lspr98/bike-computer-32/software/esp32/esp32c3-bike-companion-32/include/screens.h

#ifndef _SCREENS_H
#define _SCREENS_H

#include <Arduino.h>
#include <screenelements.h>
#include <vector>
#include <sharedspidisplay.h>
#include <globalconfig.h>

/*

    Definition of UI-screens

*/


/*

    Parent class for UI-screens

*/
class Screen {

protected:
    uint64_t _tick;
    std::vector<ScreenElement*> _elements;

public:
    Screen() : hasStatusBar(false), hasMap(false) {};
    bool hasStatusBar, hasMap;
    virtual void reset() = 0;
    virtual bool render(SharedSPIDisplay* display) = 0;
};


class BootScreen : public Screen {

private:
    int textSize = 2;
    int spinnerSize = 15;
    int rows[5] = {5, 35, 65, 95, 125};
    int cols[2] = {5, 120};

    ScreenText _labelDisplay = ScreenText(cols[0], rows[0], textSize, "Display");
    ScreenText _labelGnss = ScreenText(cols[0], rows[1], textSize, "GNSS");
    ScreenText _labelSD = ScreenText(cols[0], rows[2], textSize, "SDCard");
    ScreenText _labelMap = ScreenText(cols[0], rows[3], textSize, "Map");
    ScreenText _labelTrack = ScreenText(cols[0], rows[4], textSize, "Track");

    // Note: these labels are used as center elements for the spinners. Do not add them to the _elements list.
    ScreenText _checkDisplay = ScreenText(cols[1], rows[0], textSize, "OK");
    ScreenText _checkGnss = ScreenText(cols[1], rows[1], textSize, "OK");
    ScreenText _checkSD = ScreenText(cols[1], rows[2], textSize, "OK");
    ScreenText _checkMap = ScreenText(cols[1], rows[3], textSize, "OK");
    ScreenText _checkTrack = ScreenText(cols[1], rows[4], textSize, "OK");

    ScreenDoubleCircleSpinner _spinnerDisplay = ScreenDoubleCircleSpinner(cols[1], rows[0], spinnerSize, &_checkDisplay);
    ScreenDoubleCircleSpinner _spinnerGnss = ScreenDoubleCircleSpinner(cols[1], rows[1], spinnerSize, &_checkGnss);
    ScreenDoubleCircleSpinner _spinnerSD = ScreenDoubleCircleSpinner(cols[1], rows[2], spinnerSize, &_checkSD);
    ScreenDoubleCircleSpinner _spinnerMap = ScreenDoubleCircleSpinner(cols[1], rows[3], spinnerSize, &_checkMap);
    ScreenDoubleCircleSpinner _spinnerTrack = ScreenDoubleCircleSpinner(cols[1], rows[4], spinnerSize, &_checkTrack);

public:
    int8_t displayOK, gnssOK, mapOK, sdOK, trackOK;

    BootScreen() : Screen(), displayOK(0), gnssOK(0), mapOK(0), sdOK(0), trackOK(0) {

        _elements.push_back(&_labelDisplay);
        _elements.push_back(&_labelGnss);
        _elements.push_back(&_labelMap);
        _elements.push_back(&_labelSD);
        _elements.push_back(&_labelTrack);
        _elements.push_back(&_spinnerDisplay);
        _elements.push_back(&_spinnerGnss);
        _elements.push_back(&_spinnerMap);
        _elements.push_back(&_spinnerSD);
        _elements.push_back(&_spinnerTrack);
    };

    void reset() {

    };

    bool render(SharedSPIDisplay* display) {
        // Update elements based on status
        if(displayOK < 0) _checkDisplay.setText("ER");
        if(gnssOK < 0) _checkGnss.setText("ER");
        if(sdOK < 0) _checkSD.setText("ER");
        if(mapOK < 0) _checkMap.setText("ER");
        if(trackOK < 0) _checkTrack.setText("ER");

        _spinnerDisplay.setStatic(displayOK != 0);
        _spinnerDisplay.setCenterVisiblilty(displayOK != 0);
        _spinnerGnss.setStatic(gnssOK != 0);
        _spinnerGnss.setCenterVisiblilty(gnssOK != 0);
        _spinnerSD.setStatic(sdOK != 0);
        _spinnerSD.setCenterVisiblilty(sdOK != 0);
        _spinnerMap.setStatic(mapOK != 0);
        _spinnerMap.setCenterVisiblilty(mapOK != 0);
        _spinnerTrack.setStatic(trackOK != 0);
        _spinnerTrack.setCenterVisiblilty(trackOK != 0);

        // Render elements
        for(auto it : _elements) {
            it->step();
            it->draw(display);
        }

        return true;
    };

};

extern BootScreen BOOTSCREEN;


class FixWaitingScreen : public Screen {

private:
    int textSize = 2;
    int spinnerSize = 15;
    int rows[1] = {5};
    int cols[2] = {5, 120};

    ScreenText _waitingText = ScreenText(cols[0], rows[0], textSize, "Fixing");
    ScreenText _dummyText = ScreenText(0, 0, textSize, " ");
    ScreenDoubleCircleSpinner _aquiringSpinner = ScreenDoubleCircleSpinner(cols[1], rows[0], spinnerSize, &_dummyText);
public:

    FixWaitingScreen() : Screen() {
        hasStatusBar = true;
        _elements.push_back(&_waitingText);
        _elements.push_back(&_aquiringSpinner);
    }

    void reset() {};
    
    bool render(SharedSPIDisplay* display) {
        // Render elements
        for(auto it : _elements) {
            it->step();
            it->draw(display);
        }

        return true;
    };

    void setCenterText(char* newText) {
        return;
    }
};

extern FixWaitingScreen FIXWAITINGSCREEN;


class MapScreen : public Screen {

public:
    MapScreen() : Screen() {
        hasStatusBar = true;
        hasMap = true;
    }

    void reset() {};

    bool render(SharedSPIDisplay* display) {
        return true;
    };

};

extern MapScreen MAPSCREEN;



#endif
