lspr98/bike-computer-32/software/esp32/esp32c3-bike-companion-32/include/uirenderer.h

#ifndef _UIRENDERER_H
#define _UIRENDERER_H

#include <tileblockrenderer.h>
#include <geopositionprovider.h>
#include <sharedspidisplay.h>
#include <gnssmodule.h>
#include <screens.h>
#include <globalconfig.h>

/*

    Class for rendering UI-elements, switching screens and ticking the main-loop

*/

class UIRenderer {

    enum StatusBarElement {time, date, speed, heading, lat, lon, nsats, err};

private:
    bool _hasGNSS, _hasPositionProvider, _hasHeader, _hasDisplay, _hasTrackIn;
    unsigned long _tLastRender, _tLoopRender;
    char* _textBuffer;

    Screen* _currentScreen;

    StatusBarElement _leftStat, _rightStat;
    SharedSPIDisplay* _disp;
    GNSSModule* _gnss;
    SimpleTile::Header* _header;
    GeoPositionProvider* _posProvider;
    GPXTrack* _track;
    TileBlockRenderer _mapRenderer;

    void renderBootScreen();
    void renderInfoScreen();
    void renderStatusBar();
    void renderStat(StatusBarElement ele, char* textBuff, bool removeTerminator=false);

public:
    UIRenderer();

    bool initializeMap(SharedSPISDCard* sd);
    void setDisplay(SharedSPIDisplay* display);
    void setGNSS(GNSSModule* gnss);
    void setPositionProvider(GeoPositionProvider* positionProvider);
    void setScreen(Screen* newScreen);
    void setHeader(SimpleTile::Header* header);
    void setGPXTrackIn(GPXTrack* track);
    bool step();
    void delay(uint64_t milliseconds);
};

extern UIRenderer UIRENDERER;

#endif
